zookzook/tv-b-gone-smd/Arduino-TV-B-Gone/WORLD_IR_CODES.h

/*
TV-B-Gone for Arduino version 0.001
Ported to Arduino by Ken Shirriff, Dec 3, 2009
http://arcfn.com

The original code is:
TV-B-Gone Firmware version 1.2
 for use with ATtiny85v and v1.2 hardware
 (c) Mitch Altman + Limor Fried 2009

*/

//Codes captured from Generation 3 TV-B-Gone by Limor Fried & Mitch Altman
//table of POWER codes

#include "main.h"

const uint16_t code_na000Times[] PROGMEM = {
  60, 60,
  60, 2700,
  120, 60,
  240, 60,
};
const uint8_t code_na000Codes[] PROGMEM = {
  0xE2,
  0x20,
  0x80,
  0x78,
  0x88,
  0x20,
  0x10,
};
const struct IrCode code_na000Code PROGMEM = {
  freq_to_timerval(38400),
  26,             // # of pairs
  2,              // # of bits per index
  code_na000Times,
  code_na000Codes
};

const uint16_t code_na001Times[] PROGMEM = {
  50, 100,
  50, 200,
  50, 800,
  400, 400,
};
const uint8_t code_na001Codes[] PROGMEM = {
  0xD5,
  0x41,
  0x11,
  0x00,
  0x14,
  0x44,
  0x6D,
  0x54,
  0x11,
  0x10,
  0x01,
  0x44,
  0x45,
};
const struct IrCode code_na001Code PROGMEM = {
  freq_to_timerval(57143),
  52,		// # of pairs
  2,		// # of bits per index
  code_na001Times,
  code_na001Codes
};
const uint16_t code_na002Times[] PROGMEM = {
  42, 46,
  42, 133,
  42, 7519,
  347, 176,
  347, 177,
};
const uint8_t code_na002Codes[] PROGMEM = {
  0x60,
  0x80,
  0x00,
  0x00,
  0x00,
  0x08,
  0x00,
  0x00,
  0x00,
  0x20,
  0x00,
  0x00,
  0x04,
  0x12,
  0x48,
  0x04,
  0x12,
  0x48,
  0x2A,
  0x02,
  0x00,
  0x00,
  0x00,
  0x00,
  0x20,
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
  14, 491,
  14, 743,
  14, 4170,
};
const uint8_t code_eu131Codes[] PROGMEM = {
  0x55,
  0x55,
  0x42,
  0x55,
  0x55,
  0x41,
};
const struct IrCode code_eu131Code PROGMEM = {
  freq_to_timerval(38462),
  24,		// # of pairs
  2,		// # of bits per index
  code_eu131Times,
  code_eu131Codes
};
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
