zookzook/tv-b-gone-smd/Arduino-TV-B-Gone/main.h

#include <avr/pgmspace.h>

#define LED          PB2
#define IRLED        PB0

// We are selecting the EU Power Codes
#define EU_CODES 1

// Shortcut to insert single, non-optimized-out nop
#define NOP __asm__ __volatile__ ("nop")

// Tweak this if neccessary to change timing
#define DELAY_CNT 11

// Makes the codes more readable. the OCRA is actually
// programmed in terms of 'periods' not 'freqs' - that
// is, the inverse!
#define freq_to_timerval(x) ((F_CPU / x - 1)/ 2)

// Lets us calculate the size of the NA/EU databases
#define NUM_ELEM(x) (sizeof (x) / sizeof (*(x)));

// The structure of compressed code entries
struct IrCode {
  uint8_t timer_val;
  uint8_t numpairs;
  uint8_t bitcompression;
  uint16_t const *times;
  uint8_t const *codes;
};

void xmitCodeElement(uint16_t ontime, uint16_t offtime, uint8_t PWM_code );
void flashslowLEDx( uint8_t num_blinks );
void quickflashLEDx( uint8_t x );
void tvbgone_sleep( void );
void delay_ten_us(uint16_t us);
void quickflashLED( void );
